DJSures/FreeChaF/FreeChaF-master/src/controller.c

/*
	This file is part of FreeChaF.

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
	You should have received a copy of the GNU General Public License
	along with FreeChaF.  If not, see http://www.gnu.org/licenses/
*/

#include "controller.h"
#include "ports.h"
#include "channelf.h"

#include <stdio.h>

int State[] = {0,0,0};
int enabled = 0;

#define Console 0
#define ControlA 1
#define ControlB 2

int ConsolePort = 0;
int ControlAPort = 1;
int ControlBPort = 4;
int Swapped = 0;

void setButton(int control, int button, int pressed)
{
	/*
			// Console 
			0 // TIME
			1 // MODE
			2 // HOLD
			3 // START

			// Controller
			0 // Right
			1 // Left
			2 // Back
			3 // Forward
			4 // rot left
			5 // rot right
			6 // pull
			7 // push
	*/

	if(pressed)
	{
		State[control] |= 1<<button;
	}
	else
	{
		State[control] &= (1<<button)^0xFF;
	}
}

// DJ: public exposure for setButton
void CONTROLLER_setButton(int control, int button, int pressed) {

	setButton(control, button, pressed);
}

void CONTROLLER_setInput(int control, int state)
{
	if(control>=0 && control<=2)
	{
		State[control] = state;
	}
}

void CONTROLLER_swap()
{
	int t = ControlAPort;
	ControlAPort = ControlBPort;
	ControlBPort = t;

	Swapped ^= 1;
}

int CONTROLLER_swapped()
{
	return Swapped;
}

int CONTROLLER_portRead(int port)
{
	if(port==ConsolePort)
	{
		 return (State[Console]^0xFF) & 0x0F;
	}
	if(enabled)
	{
		if(port==ControlAPort)
		{
			return(State[ControlA]^0xFF);
		}	
		if(port==ControlBPort)
		{
			return(State[ControlB]^0xFF);
		}
	}
	return 0;
}

void CONTROLLER_portReceive(int port, int val)
{
	val &=0xFF;
	if(port==ConsolePort) // Console
	{
		enabled = (val&0x40)==0;
	}
}

// Console buttons

int cursorX = 4; // initial cursor setting 'Start' 
int cursorDown = 0;

void CONTROLLER_consoleInput(int action, int pressed)
{
	switch(action)
	{
		case 0: if(pressed) { cursorX--; } break;
		case 1: if(pressed) { cursorX++; } break;
		case 2:
			cursorDown = pressed;
			if(cursorX==0)
			{
				if(pressed) { CHANNELF_reset(); }
			}
			else
			{
				setButton(0, cursorX-1, pressed);
			}
			break;
	}

	if (cursorX<0) { cursorX = 4; }
	if (cursorX>4) { cursorX = 0; }
}

int CONTROLLER_cursorPos()
{
	return cursorX;
}
int CONTROLLER_cursorDown()
{
	return cursorDown;
}
